meadiode/vin_display/src/command.h

#ifndef __COMMAND_H
#define __COMMAND_H


#define COMMAND_DISPLAY_TEXT   10
#define COMMAND_SET_BRIGHTNESS 11
#define COMMAND_KNOB_EVENT     12
#define COMMAND_BUTTON_EVENT   13
#define COMMAND_BUZZER_PLAY    14
#define COMMAND_BUZZER_QUEUE   15
#define COMMAND_BUZZER_EVENT   16


void command_init(void);


#endif /* __COMMAND_H */
